Ksv047/estacao_meteorologica_baixo_custo/data/painel_thingsboard.png

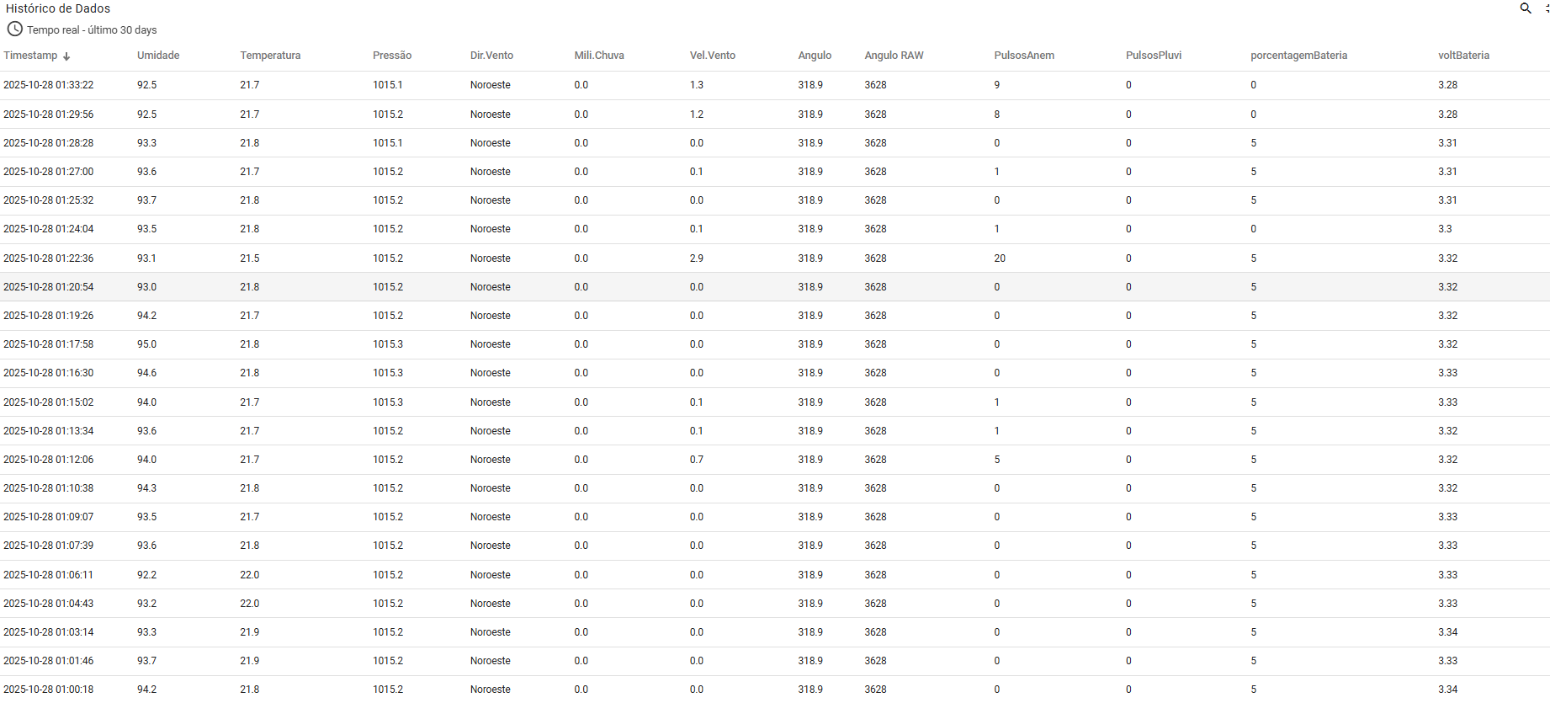
data/painel_thingsboard.png
