Ksv047/estacao_meteorologica_baixo_custo/hardware/3D_MODELS/PeçaBaixaSuportePainelSolar.stl

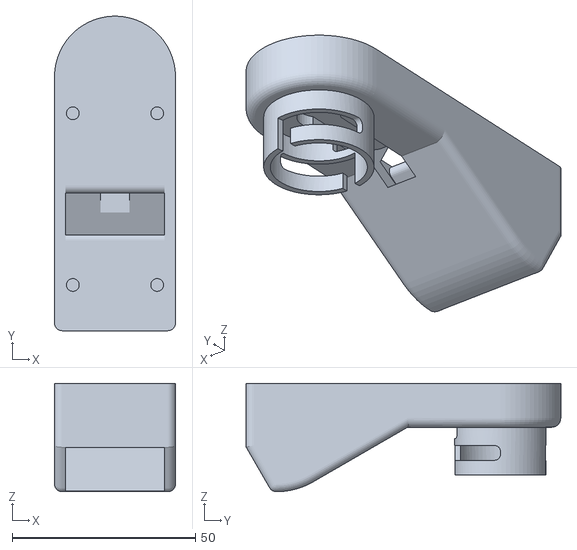
[picture p37: CAD file, 2025-11-04]
hardware/3D_MODELS/PeçaBaixaSuportePainelSolar.stl
33.0 x 85.8 x 29.6
