Ksv047/estacao_meteorologica_baixo_custo/hardware/3D_MODELS/PontaFrenteDirVento.stl

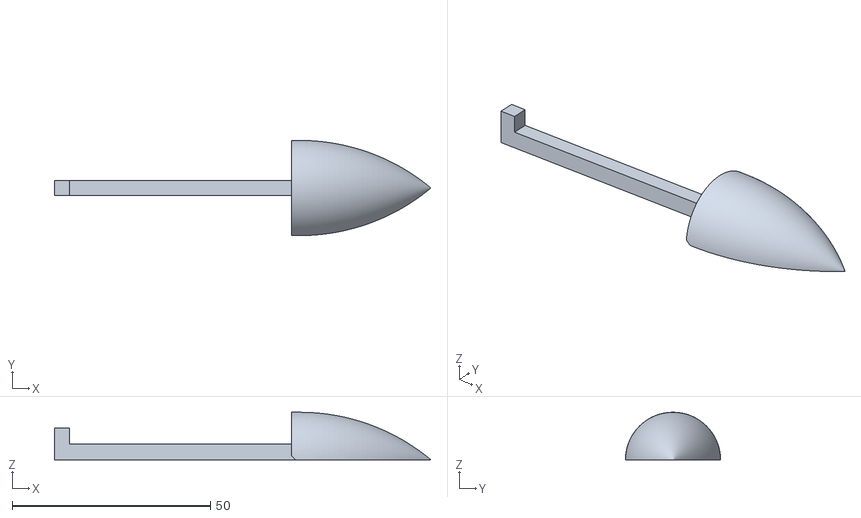
[picture p38: CAD file, 2025-11-04]
hardware/3D_MODELS/PontaFrenteDirVento.stl
94.8 x 24.0 x 12.0
