Ksv047/estacao_meteorologica_baixo_custo/hardware/3D_MODELS/PluviometroCorpo.stl

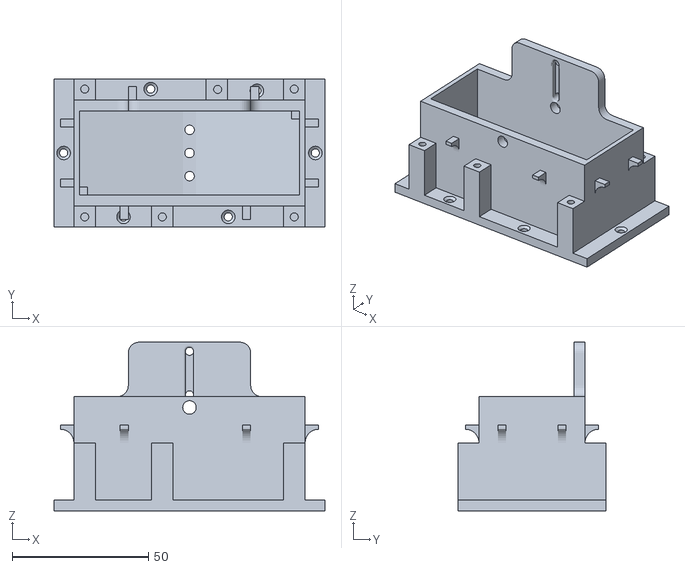
[picture p39: CAD file, 2025-11-04]
hardware/3D_MODELS/PluviometroCorpo.stl
99.6 x 54.4 x 62.0
