Ksv047/estacao_meteorologica_baixo_custo/hardware/3D_MODELS/SuporteSensoresBaixo.stl

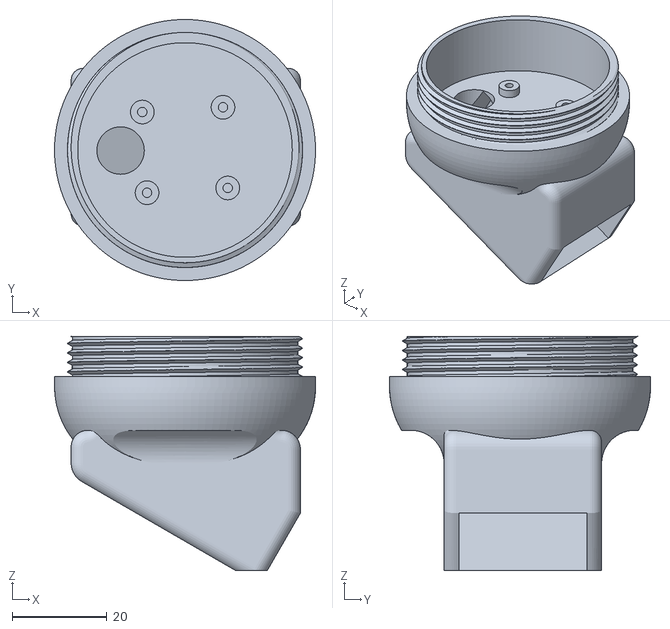
[picture p40: CAD file, 2025-11-04]
hardware/3D_MODELS/SuporteSensoresBaixo.stl
55.0 x 55.0 x 49.4
