Ksv047/estacao_meteorologica_baixo_custo/hardware/3D_MODELS/EixoVelVento.stl

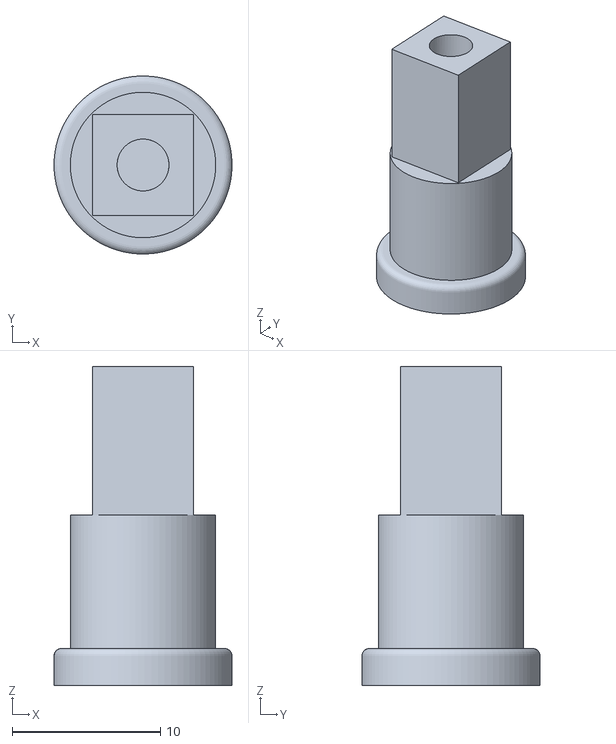
[picture p41: CAD file, 2025-11-04]
hardware/3D_MODELS/EixoVelVento.stl
12.0 x 12.0 x 21.5
