Ksv047/estacao_meteorologica_baixo_custo/hardware/3D_MODELS/PluviometroFunil.stl

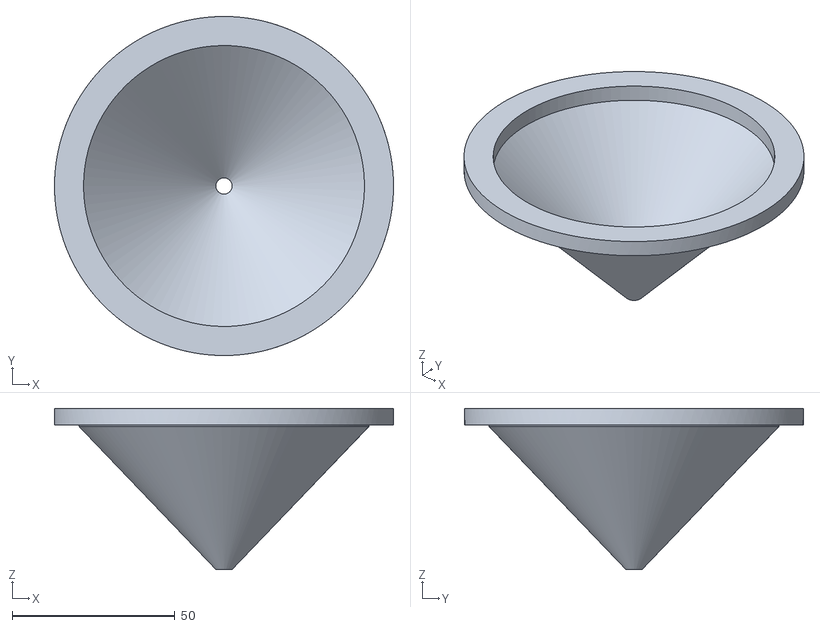
[picture p42: CAD file, 2025-11-04]
hardware/3D_MODELS/PluviometroFunil.stl
104.0 x 104.0 x 49.4
